TimGremalm/LightBoxNano/output/LightBoxNano_Back.png

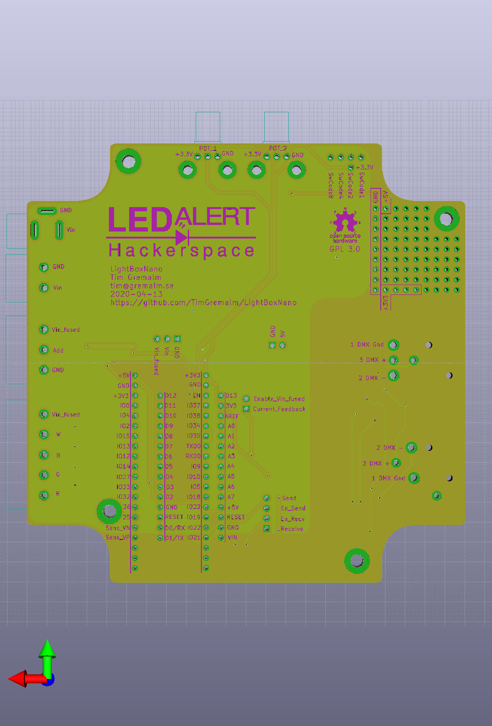
output/LightBoxNano_Back.png
