TimGremalm/LightBoxNano/output/LightBoxNano_Front.png

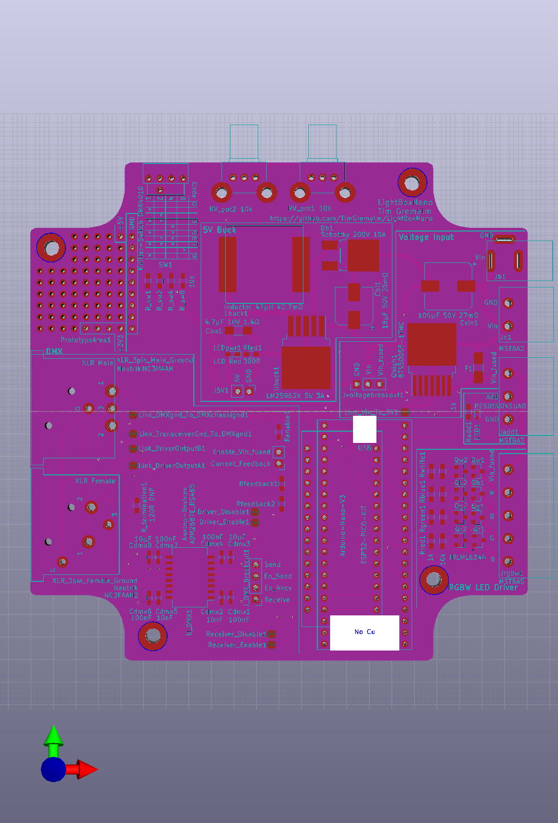
output/LightBoxNano_Front.png
